Andreasdahlberg/sillycat/hardware/node_unit_exterior/standard_components/aa_battery.SLDPRT

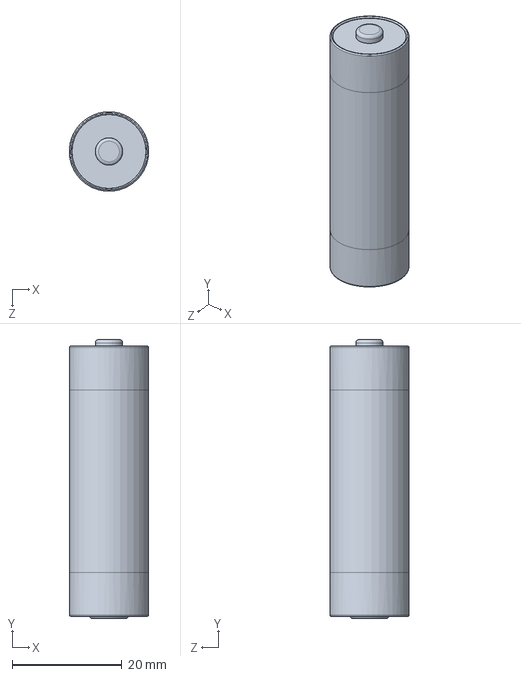
[picture p21: CAD file, 2015-09-07]
hardware/node_unit_exterior/standard_components/aa_battery.SLDPRT
14.5 x 50.9 x 14.5 mm
