Andreasdahlberg/sillycat/hardware/main_unit_exterior/electrical_components/male_header_20.SLDPRT

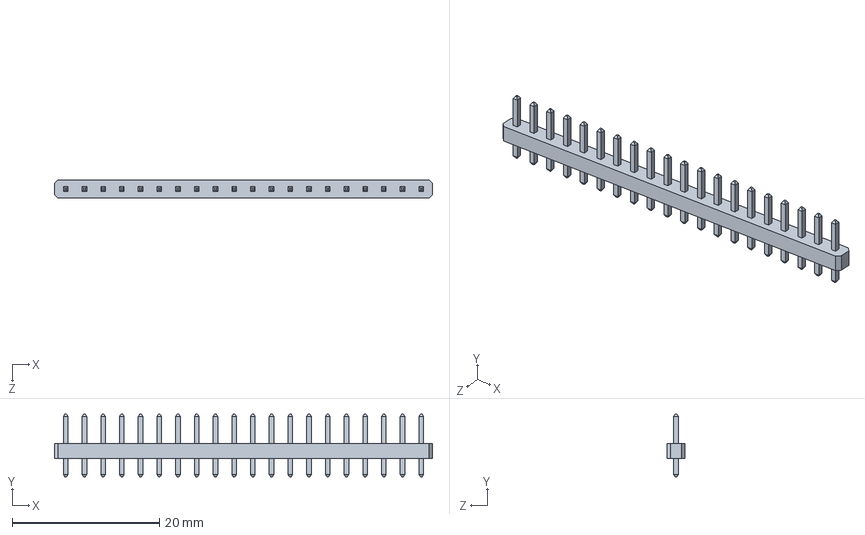
[picture p22: CAD file, 2014-12-17]
hardware/main_unit_exterior/electrical_components/male_header_20.SLDPRT
51.3 x 8.50 x 2.50 mm
