Andreasdahlberg/sillycat/hardware/main_unit_exterior/mechanical_components/front_casing.SLDPRT

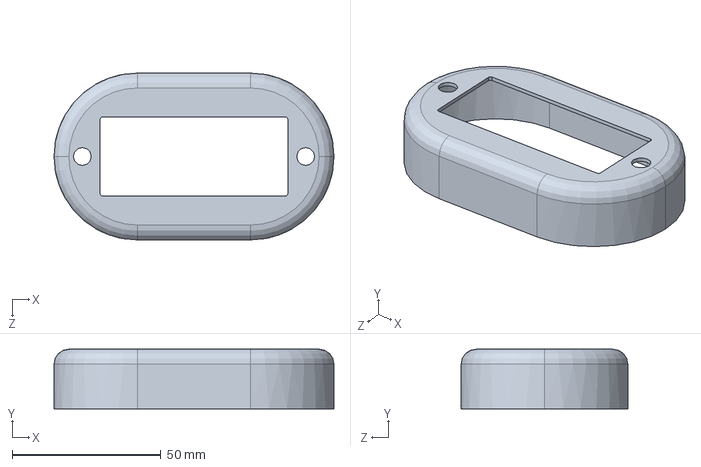
[picture p23: CAD file, 2014-12-17]
hardware/main_unit_exterior/mechanical_components/front_casing.SLDPRT
94.0 x 20.0 x 56.0 mm
