Andreasdahlberg/sillycat/hardware/node_unit_exterior/production_files/casing_end_cover_usb.STL

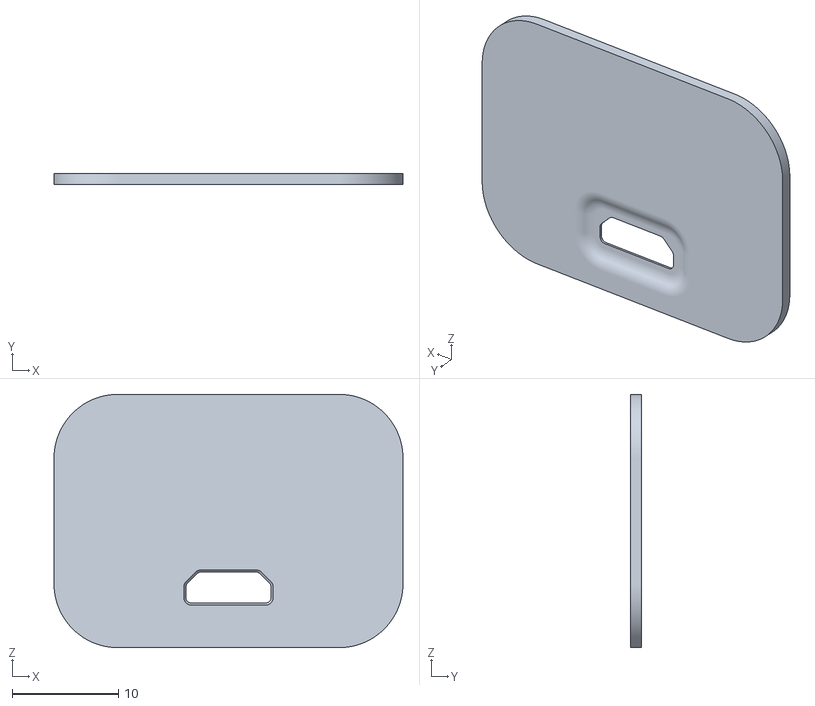
[picture p24: CAD file, 2014-09-30]
hardware/node_unit_exterior/production_files/casing_end_cover_usb.STL
32.8 x 1.00 x 23.8
