Andreasdahlberg/sillycat/hardware/main_unit_exterior/electrical_components/TO-220.SLDPRT

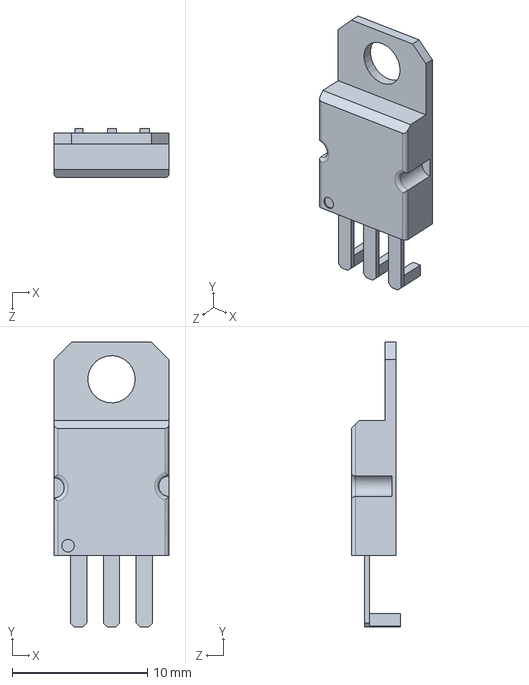
[picture p25: CAD file, 2014-12-17]
hardware/main_unit_exterior/electrical_components/TO-220.SLDPRT
8.50 x 21.1 x 3.66 mm
