Andreasdahlberg/sillycat/hardware/node_unit_exterior/production_files/casing_casing_upper.STL

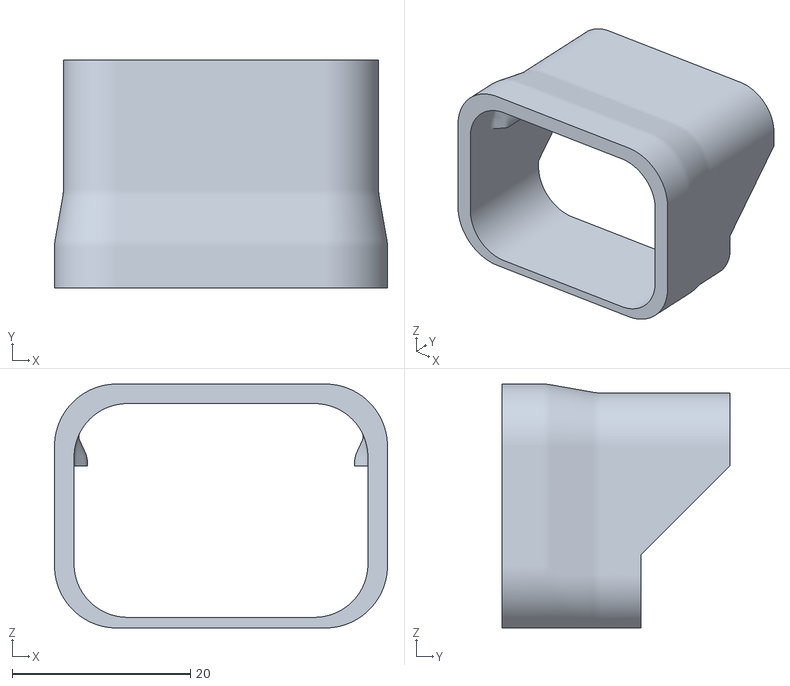
[picture p26: CAD file, 2014-09-30]
hardware/node_unit_exterior/production_files/casing_casing_upper.STL
37.4 x 25.6 x 27.4
