Andreasdahlberg/sillycat/hardware/node_unit_exterior/standard_components/SMA_antenna.SLDPRT

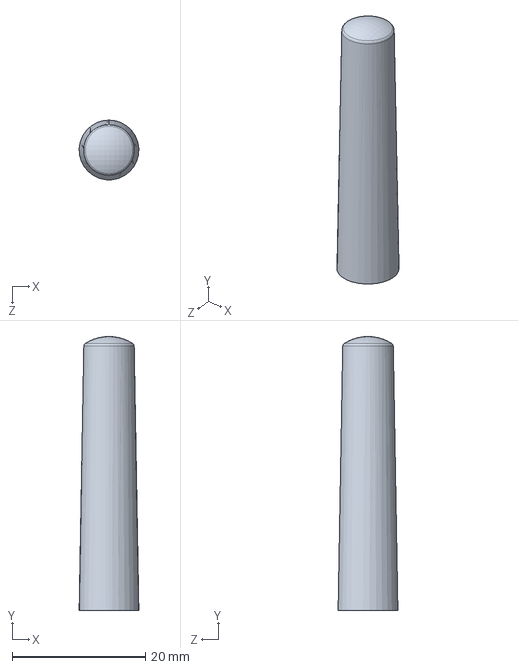
[picture p27: CAD file, 2015-09-06]
hardware/node_unit_exterior/standard_components/SMA_antenna.SLDPRT
8.99 x 41.2 x 9.00 mm
