Andreasdahlberg/sillycat/hardware/main_unit_exterior/electrical_components/NHD_223_OLED_display.SLDPRT

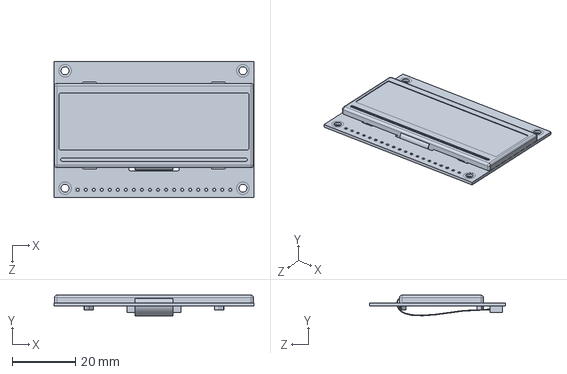
[picture p28: CAD file, 2014-12-17]
hardware/main_unit_exterior/electrical_components/NHD_223_OLED_display.SLDPRT
63.2 x 6.53 x 43.1 mm
