Andreasdahlberg/sillycat/hardware/node_unit_exterior/end_plug_cover.SLDPRT

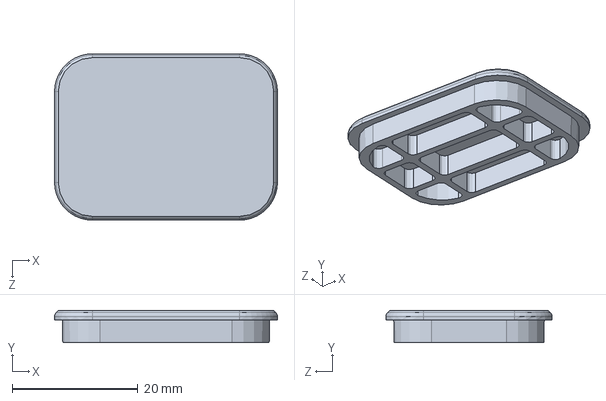
[picture p29: CAD file, 2015-09-07]
hardware/node_unit_exterior/end_plug_cover.SLDPRT
35.4 x 5.10 x 26.4 mm
