Andreasdahlberg/sillycat/hardware/node_unit_exterior/standard_components/DPAK.SLDPRT

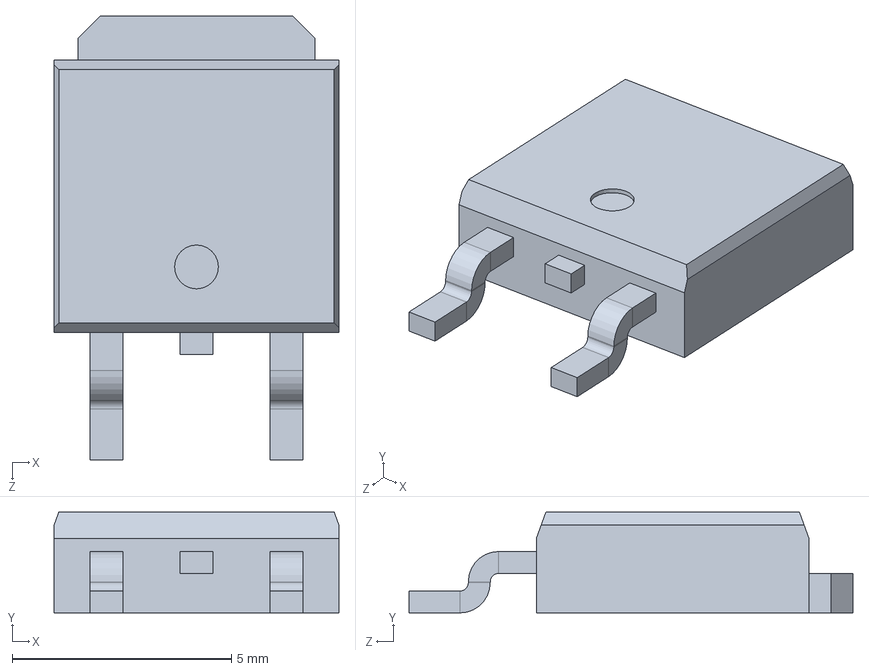
[picture p30: CAD file, 2015-09-06]
hardware/node_unit_exterior/standard_components/DPAK.SLDPRT
6.50 x 2.30 x 10.1 mm
