Andreasdahlberg/sillycat/hardware/node_unit_exterior/end_cover_usb.SLDPRT

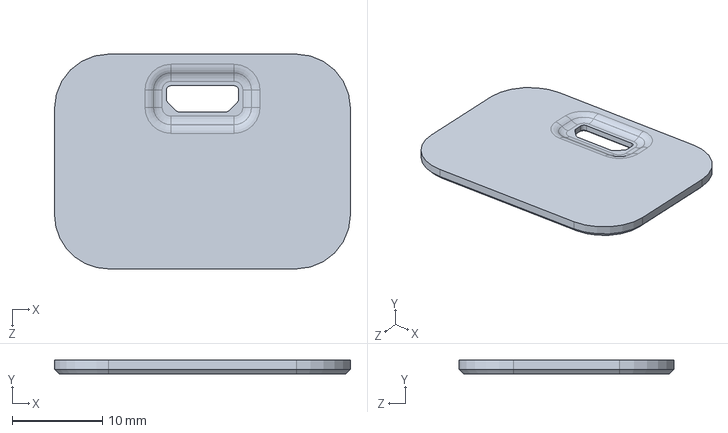
[picture p31: CAD file, 2015-09-07]
hardware/node_unit_exterior/end_cover_usb.SLDPRT
32.8 x 1.50 x 23.8 mm
