Andreasdahlberg/sillycat/hardware/node_unit_exterior/standard_components/nfc_tag.SLDPRT

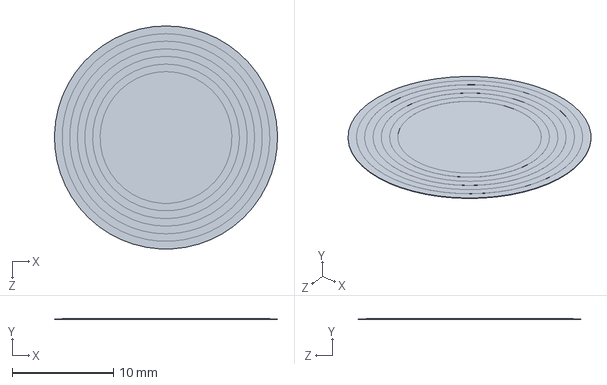
[picture p32: CAD file, 2015-09-05]
hardware/node_unit_exterior/standard_components/nfc_tag.SLDPRT
22.0 x 0.06 x 22.0 mm
