Andreasdahlberg/sillycat/hardware/node_unit_exterior/casing_lower.SLDPRT

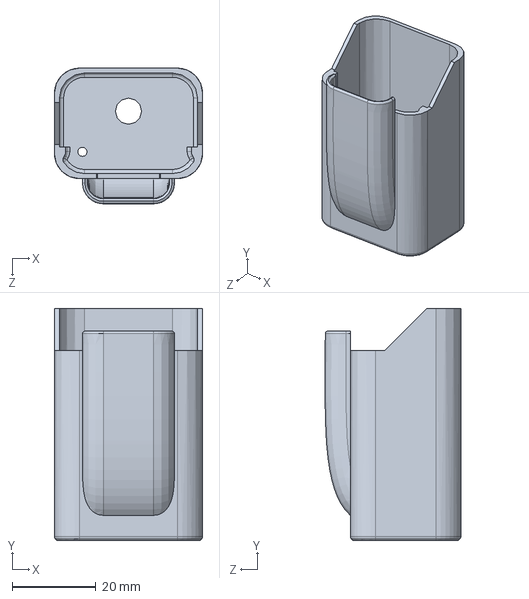
[picture p33: CAD file, 2015-09-05]
hardware/node_unit_exterior/casing_lower.SLDPRT
35.4 x 55.4 x 32.4 mm
