Andreasdahlberg/sillycat/hardware/node_unit_exterior/standard_components/wago_2059_303_casing.SLDPRT

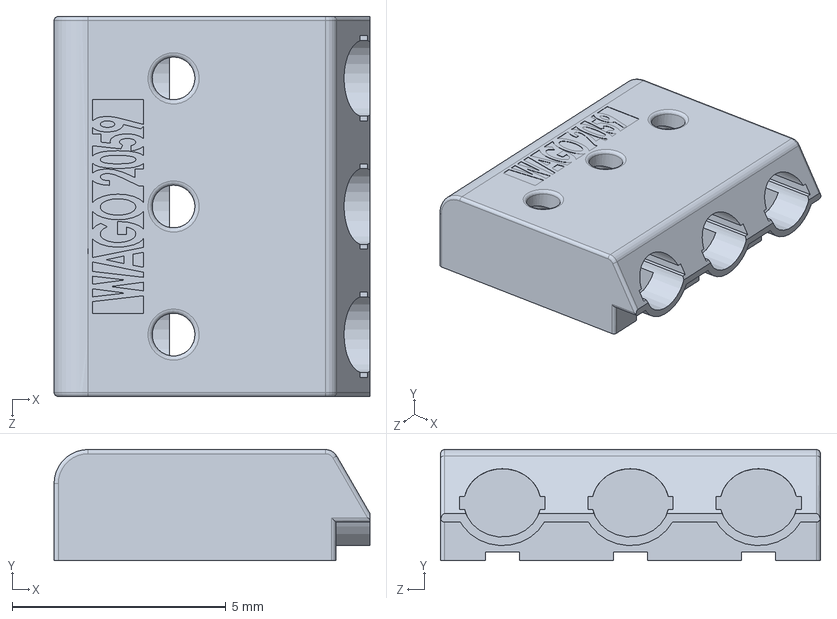
[picture p34: CAD file, 2015-09-05]
hardware/node_unit_exterior/standard_components/wago_2059_303_casing.SLDPRT
7.40 x 2.60 x 8.90 mm
