Andreasdahlberg/sillycat/hardware/node_unit_exterior/casing_upper.SLDPRT

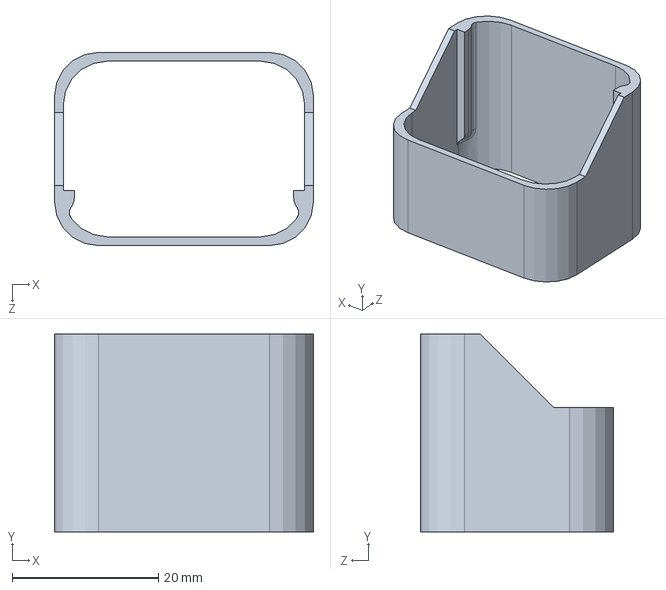
[picture p35: CAD file, 2015-09-05]
hardware/node_unit_exterior/casing_upper.SLDPRT
35.4 x 27.0 x 26.4 mm
