Andreasdahlberg/sillycat/hardware/node_unit_exterior/standard_components/wago_2059_303_pin.SLDPRT

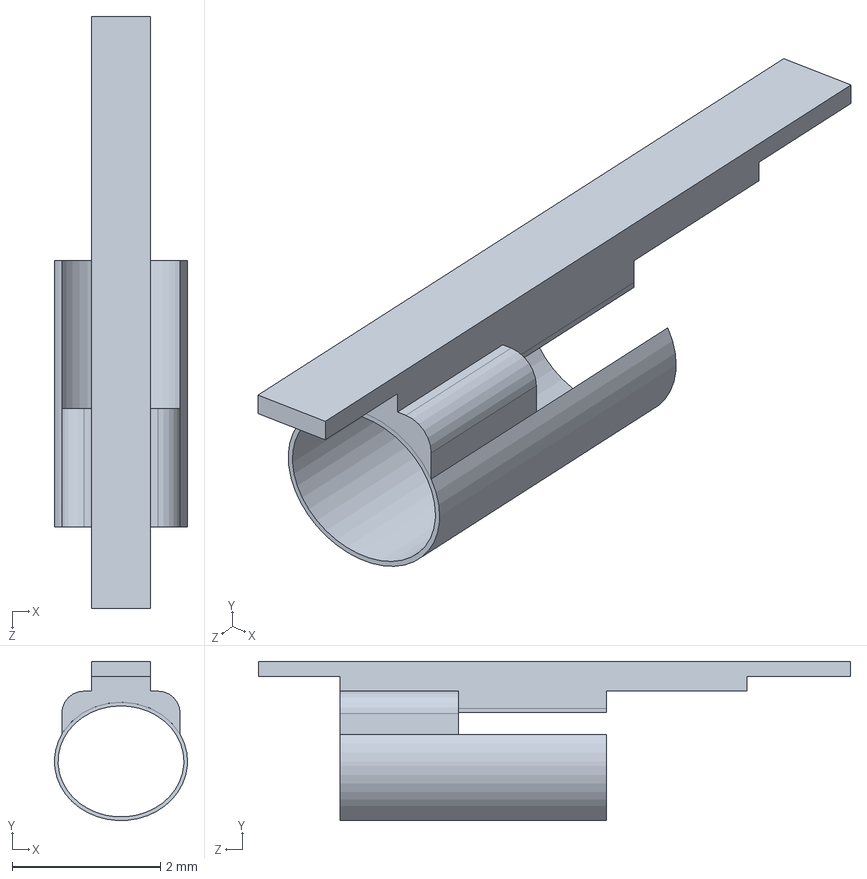
[picture p36: CAD file, 2015-09-05]
hardware/node_unit_exterior/standard_components/wago_2059_303_pin.SLDPRT
1.80 x 2.15 x 8.00 mm
