Andreasdahlberg/sillycat/hardware/node_unit_exterior/dht11_pcb.SLDPRT

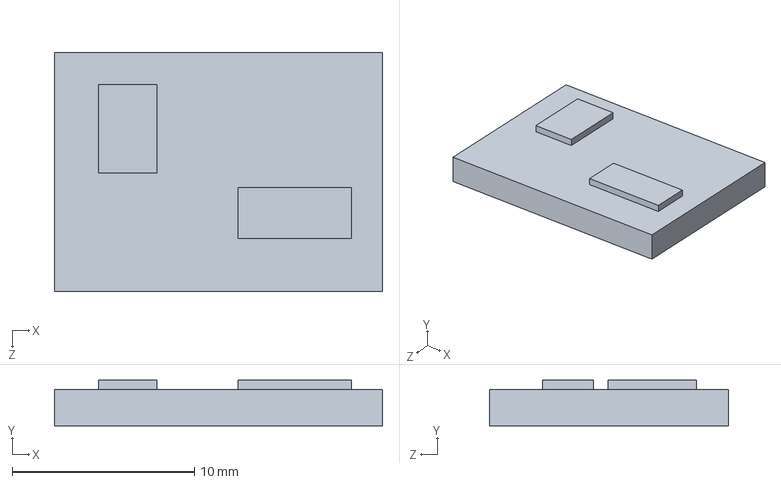
[picture p37: CAD file, 2015-09-05]
hardware/node_unit_exterior/dht11_pcb.SLDPRT
18.0 x 2.50 x 13.1 mm
