Andreasdahlberg/sillycat/hardware/node_unit_exterior/standard_components/micro usb02.SLDPRT

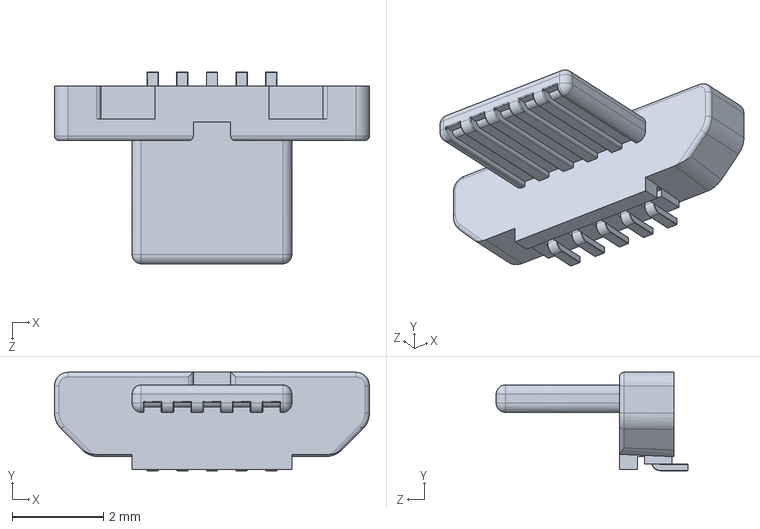
[picture p38: CAD file, 2015-09-05]
hardware/node_unit_exterior/standard_components/micro usb02.SLDPRT
6.90 x 2.16 x 4.20 mm
