Andreasdahlberg/sillycat/hardware/node_unit_exterior/dht11_body.SLDPRT

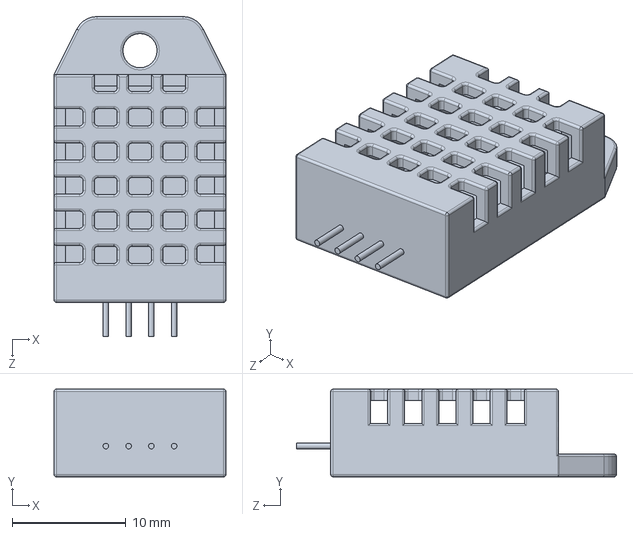
[picture p39: CAD file, 2015-09-05]
hardware/node_unit_exterior/dht11_body.SLDPRT
15.1 x 7.70 x 28.1 mm
