Andreasdahlberg/sillycat/hardware/node_unit_exterior/pcb.SLDPRT

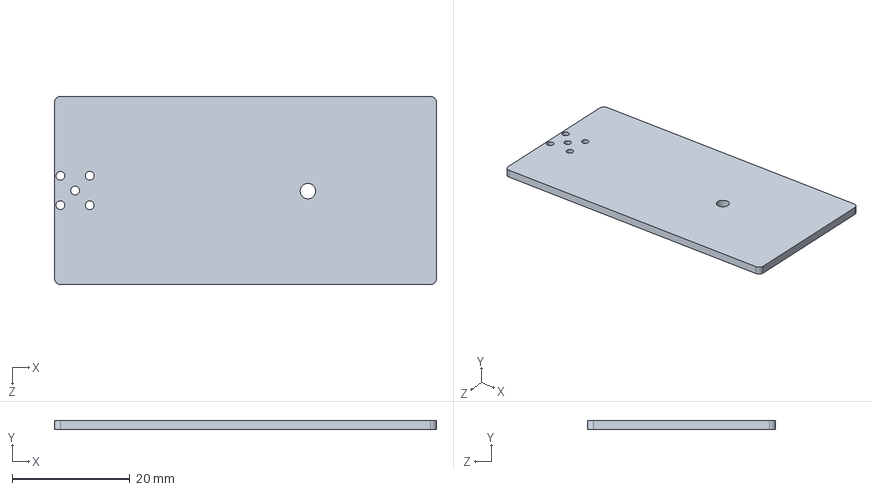
[picture p40: CAD file, 2015-09-05]
hardware/node_unit_exterior/pcb.SLDPRT
65.0 x 1.60 x 32.0 mm
