Andreasdahlberg/sillycat/hardware/node_unit_exterior/standard_components/spring.SLDPRT

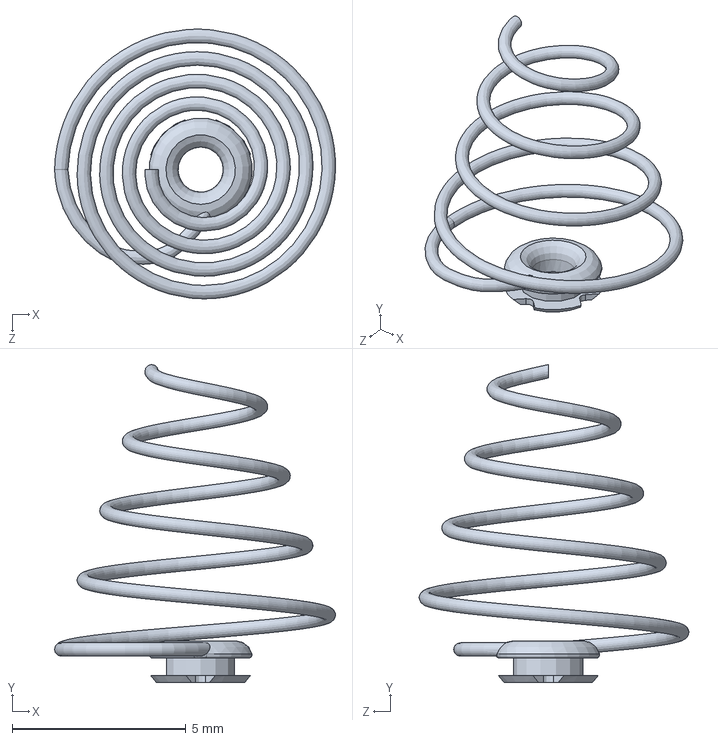
[picture p41: CAD file, 2015-09-05]
hardware/node_unit_exterior/standard_components/spring.SLDPRT
8.08 x 9.14 x 7.76 mm
