Andreasdahlberg/sillycat/hardware/node_unit_exterior/standard_components/end_plug.SLDPRT

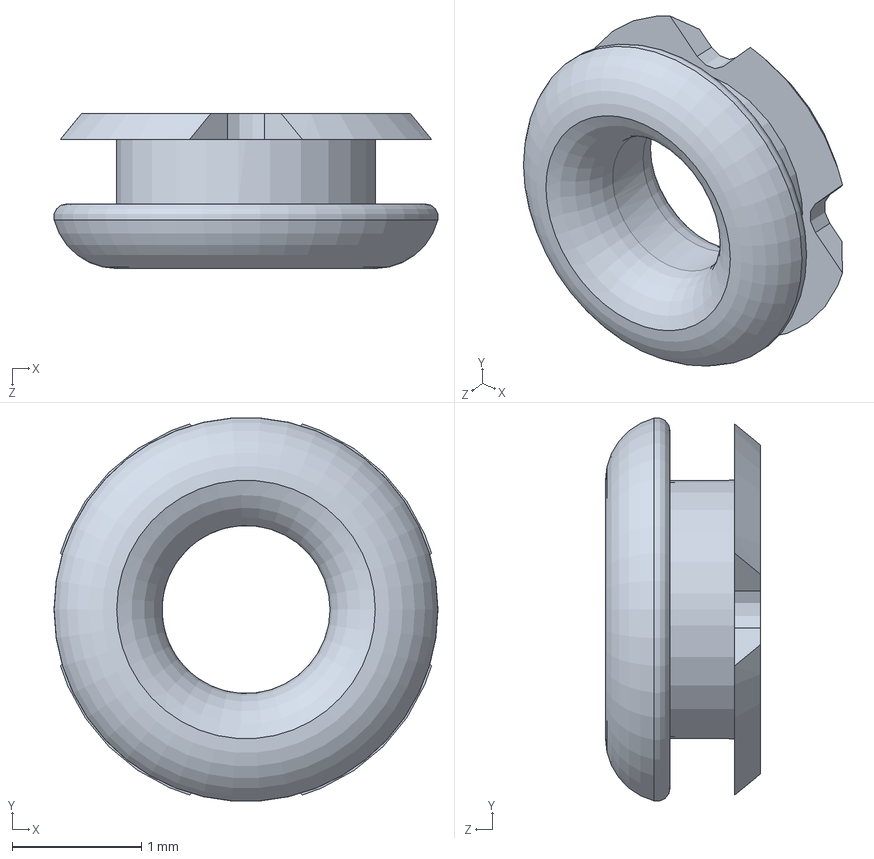
[picture p42: CAD file, 2015-09-05]
hardware/node_unit_exterior/standard_components/end_plug.SLDPRT
2.97 x 2.96 x 1.20 mm
