Andreasdahlberg/sillycat/hardware/node_unit_exterior/rfm69hw.SLDPRT

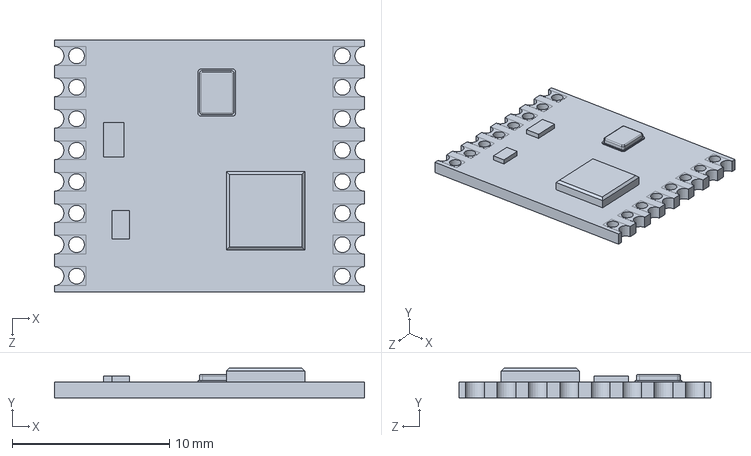
[picture p43: CAD file, 2015-09-05]
hardware/node_unit_exterior/rfm69hw.SLDPRT
19.7 x 1.90 x 16.0 mm
