Andreasdahlberg/sillycat/hardware/node_unit_exterior/standard_components/resistor_1206.SLDPRT

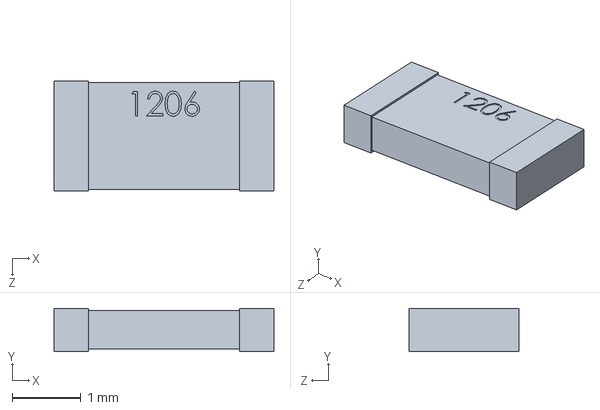
[picture p44: CAD file, 2015-09-05]
hardware/node_unit_exterior/standard_components/resistor_1206.SLDPRT
3.20 x 0.63 x 1.60 mm
