Andreasdahlberg/sillycat/hardware/node_unit_exterior/led_diffuser.SLDPRT

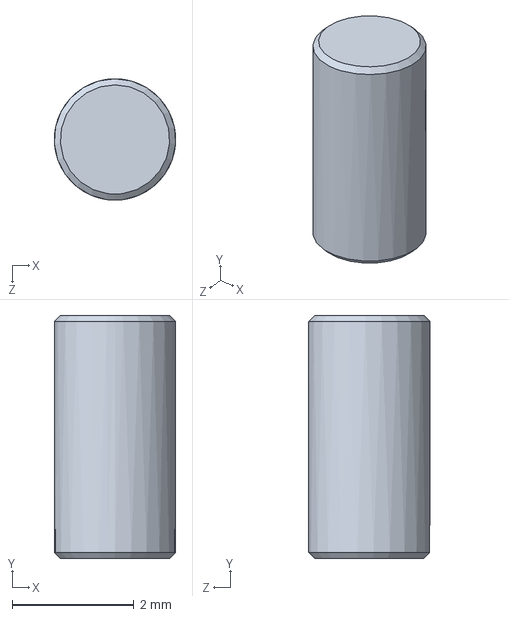
[picture p45: CAD file, 2015-09-05]
hardware/node_unit_exterior/led_diffuser.SLDPRT
2.00 x 4.00 x 2.00 mm
