Andreasdahlberg/sillycat/hardware/node_unit_exterior/standard_components/cap1206.SLDPRT

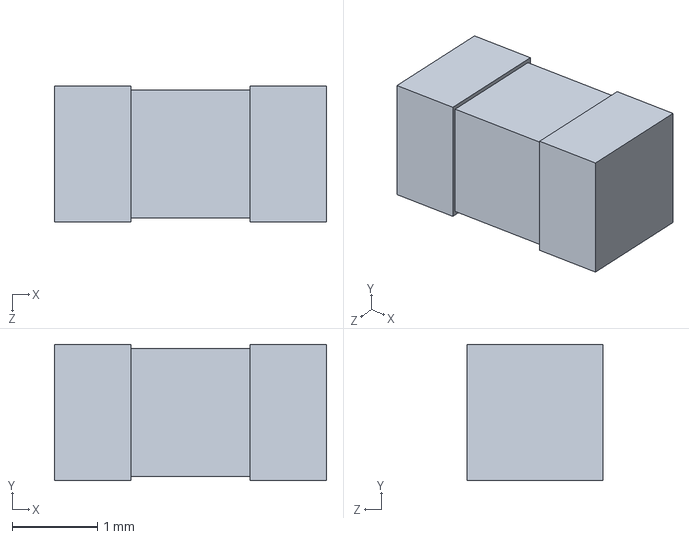
[picture p46: CAD file, 2015-09-05]
hardware/node_unit_exterior/standard_components/cap1206.SLDPRT
3.20 x 1.60 x 1.60 mm
