Andreasdahlberg/sillycat/hardware/node_unit_exterior/standard_components/spring_pin.SLDPRT

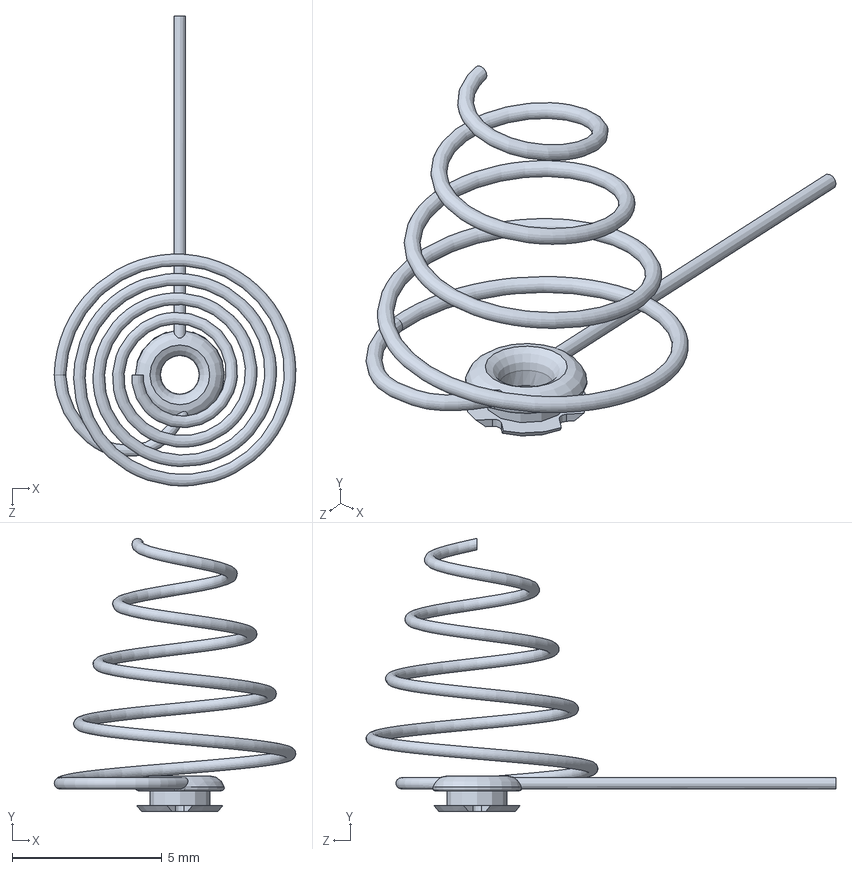
[picture p47: CAD file, 2015-09-05]
hardware/node_unit_exterior/standard_components/spring_pin.SLDPRT
8.08 x 9.14 x 15.7 mm
