Andreasdahlberg/sillycat/hardware/node_unit_exterior/standard_components/TQFP-32.SLDPRT

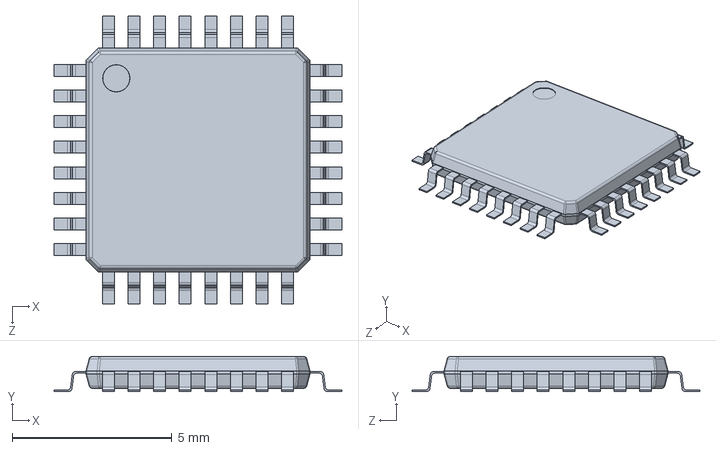
[picture p48: CAD file, 2015-09-05]
hardware/node_unit_exterior/standard_components/TQFP-32.SLDPRT
9.00 x 1.10 x 9.00 mm
