Andreasdahlberg/sillycat/hardware/node_unit_exterior/standard_components/SMA-angled.SLDPRT

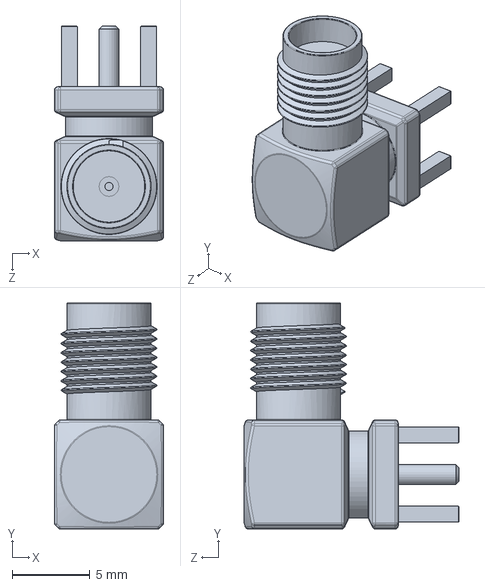
[picture p49: CAD file, 2015-09-05]
hardware/node_unit_exterior/standard_components/SMA-angled.SLDPRT
7.00 x 14.5 x 13.8 mm
