Andreasdahlberg/sillycat/hardware/node_unit_exterior/standard_components/1206_led_blue.SLDPRT

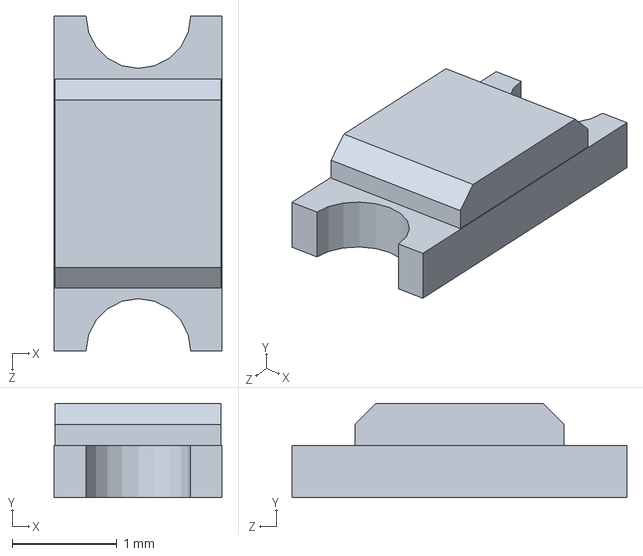
[picture p50: CAD file, 2015-09-05]
hardware/node_unit_exterior/standard_components/1206_led_blue.SLDPRT
1.60 x 0.9 x 3.20 mm
