Andreasdahlberg/sillycat/hardware/node_unit_exterior/standard_components/battery_holder_body.SLDPRT

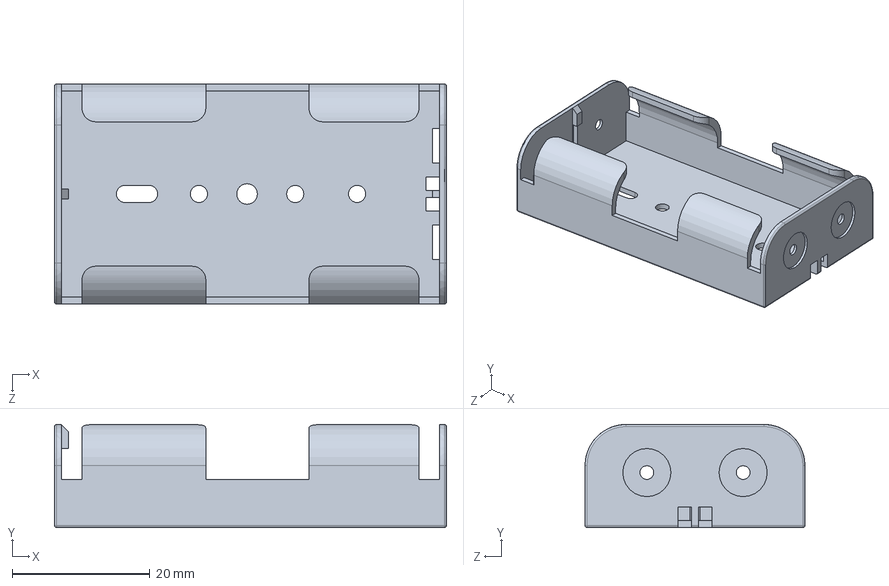
[picture p51: CAD file, 2015-09-05]
hardware/node_unit_exterior/standard_components/battery_holder_body.SLDPRT
57.0 x 15.0 x 32.0 mm
