Andreasdahlberg/sillycat/hardware/node_unit_exterior/standard_components/end_plug_pin.SLDPRT

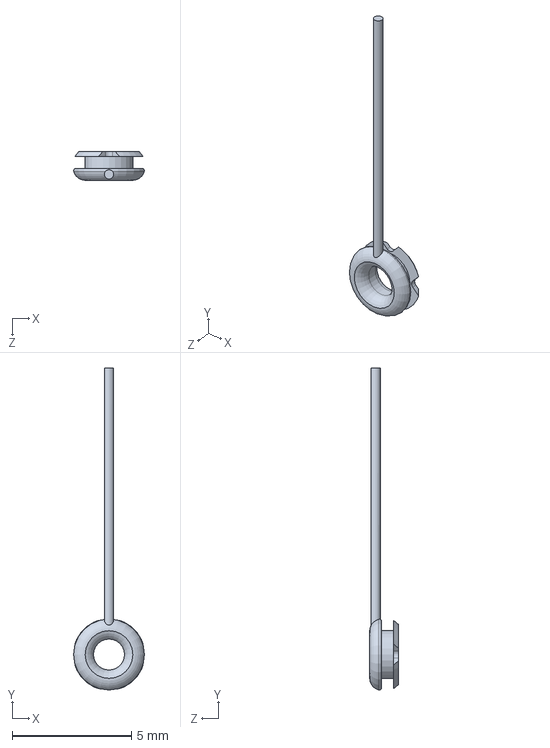
[picture p52: CAD file, 2015-09-05]
hardware/node_unit_exterior/standard_components/end_plug_pin.SLDPRT
2.97 x 13.5 x 1.20 mm
