Andreasdahlberg/sillycat/hardware/node_unit_exterior/standard_components/heatsink_V5618A.SLDPRT

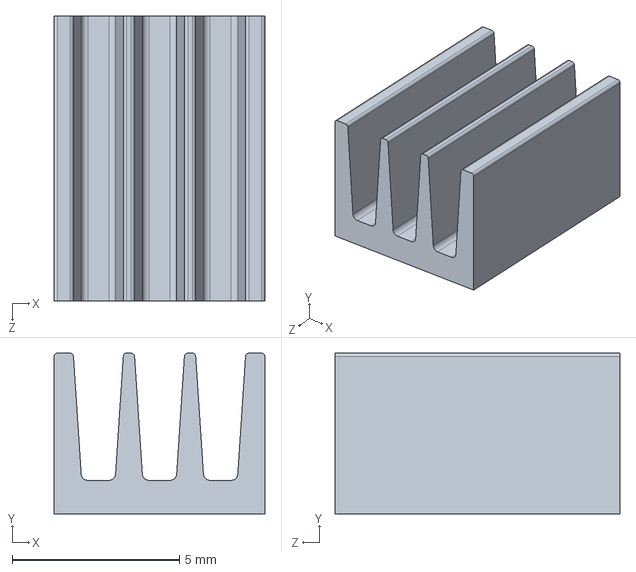
[picture p53: CAD file, 2015-09-05]
hardware/node_unit_exterior/standard_components/heatsink_V5618A.SLDPRT
6.30 x 4.80 x 8.50 mm
