Andreasdahlberg/sillycat/hardware/node_unit_exterior/standard_components/isp_header_6pin.SLDPRT

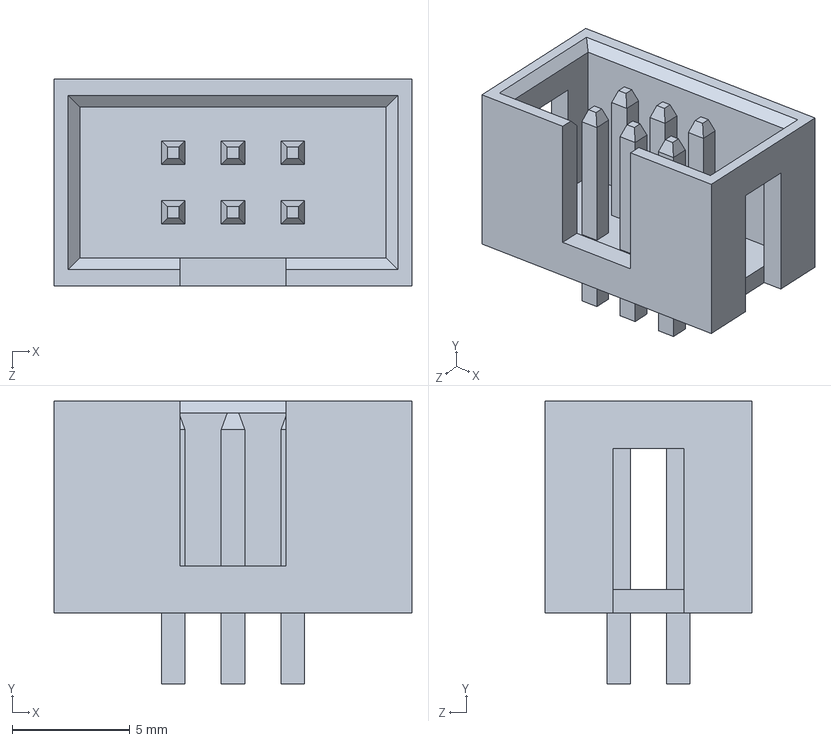
[picture p54: CAD file, 2014-09-03]
hardware/node_unit_exterior/standard_components/isp_header_6pin.SLDPRT
15.2 x 12.0 x 8.80 mm
