Andreasdahlberg/sillycat/hardware/node_unit_exterior/standard_components/USB-Mini-B.SLDPRT

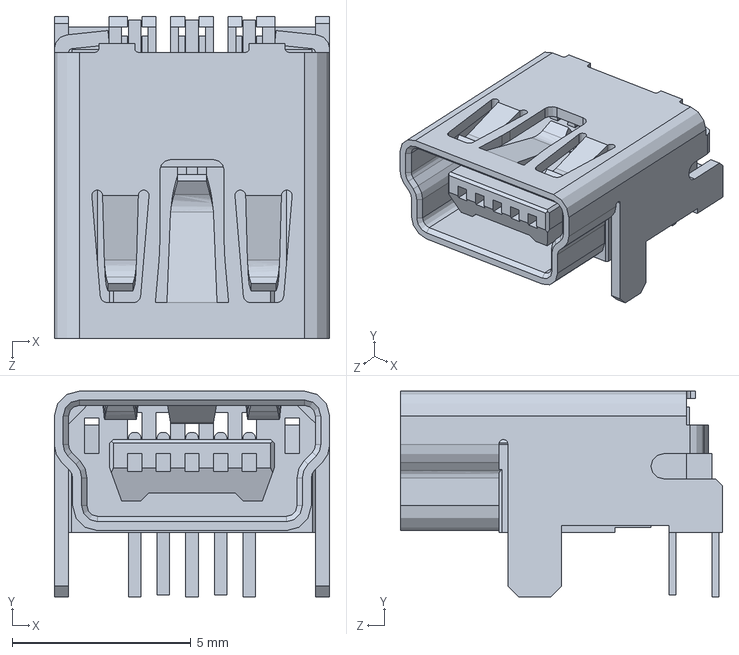
[picture p55: CAD file, 2014-09-03]
hardware/node_unit_exterior/standard_components/USB-Mini-B.SLDPRT
7.70 x 5.75 x 9.00 mm
