Andreasdahlberg/sillycat/firmware/src/main/driver/NTC/driverNTC.c

/**
 * @file   driverNTC.c
 * @Author Andreas Dahlberg (andreas.dahlberg90@gmail.com)
 * @date   2021-04-12 (Last edit)
 * @brief  NTC sensor driver
 *
 * Driver for NTC sensors.
 */

/*
This file is part of SillyCat firmware.

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
You should have received a copy of the GNU General Public License
along with SillyCat firmware.  If not, see <http://www.gnu.org/licenses/>.
*/

//////////////////////////////////////////////////////////////////////////
//INCLUDES
//////////////////////////////////////////////////////////////////////////

//NOTE: Include before all other headers
#include "common.h"

#include <avr/pgmspace.h>
#include "ADC.h"
#include "Sensor.h"
#include "Timer.h"
#include "Filter.h"
#include "libDebug.h"
#include "driverNTC.h"

//////////////////////////////////////////////////////////////////////////
//DEFINES
//////////////////////////////////////////////////////////////////////////

#define SAMPLE_PERIOD_MS 100
#define LUT_SIZE 819

//////////////////////////////////////////////////////////////////////////
//TYPE DEFINITIONS
//////////////////////////////////////////////////////////////////////////

enum lookup_table_type {GENERIC, MF52};

struct ntc_sensor_t
{
    struct sensor_t base;
    struct
    {
        struct adc_channel_t channel;
        uint8_t index;
    } adc;
    struct filter_t filter;
    uint32_t timer;
    enum lookup_table_type lut_type;
};

struct lookup_table_t
{
    uint16_t offset;
    uint16_t temperatures[LUT_SIZE];
};

//////////////////////////////////////////////////////////////////////////
//LOCAL FUNCTION PROTOTYPES
//////////////////////////////////////////////////////////////////////////

static void Update(struct sensor_t *super_p);
static bool GetTemperature(struct ntc_sensor_t *self_p, int16_t *temperature_p);
static bool ADCValueToTemperature(uint16_t adc_value, int16_t *temperature_p, size_t lut_index);
static bool IsValid(uint16_t adc_value, size_t lut_index);
static int16_t FilterTemperature(struct ntc_sensor_t *self_p, int16_t temperature);

//////////////////////////////////////////////////////////////////////////
//VARIABLES
//////////////////////////////////////////////////////////////////////////

static const struct lookup_table_t ntc_lut[2] PROGMEM =
{
    {
        .offset = 120,
        .temperatures = {
            -201, -199, -197, -195, -194, -192, -190, -188, -187, -185, -183, -181, -180, -178,
                -176, -175, -173, -172, -170, -168, -167, -165, -163, -162, -160, -159, -157, -156,
                -154, -152, -151, -149, -148, -146, -145, -143, -142, -140, -139, -137, -136, -134,
                -133, -131, -130, -129, -127, -126, -124, -123, -121, -120, -119, -117, -116, -114,
                -113, -112, -110, -109, -107, -106, -105, -103, -102, -101, -99, -98, -97, -95, -94,
                -93, -91, -90, -89, -87, -86, -85, -83, -82, -81, -79, -78, -77, -76, -74, -73, -72,
                -71, -69, -68, -67, -66, -64, -63, -62, -61, -59, -58, -57, -56, -54, -53, -52, -51,
                -50, -48, -47, -46, -45, -43, -42, -41, -40, -39, -38, -36, -35, -34, -33, -32, -30,
                -29, -28, -27, -26, -25, -23, -22, -21, -20, -19, -18, -17, -15, -14, -13, -12, -11,
                -10, -9, -7, -6, -5, -4, -3, -2, -1, 0, 2, 3, 4, 5, 6, 7, 8, 9, 10, 11, 13, 14, 15, 16,
                17, 18, 19, 20, 21, 22, 23, 25, 26, 27, 28, 29, 30, 31, 32, 33, 34, 35, 36, 37, 39, 40,
                41, 42, 43, 44, 45, 46, 47, 48, 49, 50, 51, 52, 53, 54, 55, 56, 57, 59, 60, 61, 62, 63,
                64, 65, 66, 67, 68, 69, 70, 71, 72, 73, 74, 75, 76, 77, 78, 79, 80, 81, 82, 83, 84, 85,
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
            .Update = Update
        },
        .adc = {
            .index = 0x06
        },
        .lut_type = GENERIC
    },
    {
        .base =
        {
            .Update = Update
        },
        .adc = {
            .index = 0x07
        },
        .lut_type = MF52
    }
};

//////////////////////////////////////////////////////////////////////////
//FUNCTIONS
//////////////////////////////////////////////////////////////////////////

void driverNTC_Init(void)
{
    for (size_t i = 0; i < ElementsIn(ntc_sensors); ++i)
    {
        ADC_InitChannel(&ntc_sensors[i].adc.channel, ntc_sensors[i].adc.index);
    }

    INFO("NTC sensors initialized");
}

struct sensor_t *driverNTC_GetSensor(size_t id)
{
    sc_assert(id < ElementsIn(ntc_sensors));

    return (struct sensor_t *)&ntc_sensors[id];
}

//////////////////////////////////////////////////////////////////////////
//LOCAL FUNCTIONS
//////////////////////////////////////////////////////////////////////////

static void Update(struct sensor_t *super_p)
{
    struct ntc_sensor_t *self_p = (struct ntc_sensor_t *)super_p;

    if (Timer_TimeDifference(self_p->timer) > SAMPLE_PERIOD_MS)
    {
        int16_t temperature;

        if (GetTemperature(self_p, &temperature))
        {
            self_p->base.value = FilterTemperature(self_p, temperature);
            self_p->base.valid = true;
        }
        else
        {
            self_p->base.valid = false;
        }

        self_p->timer = Timer_GetMilliseconds();
    }
}

static bool GetTemperature(struct ntc_sensor_t *self_p, int16_t *temperature_p)
{
    uint16_t adc_value;

    ADC_Convert(&self_p->adc.channel, &adc_value, 1);
    return ADCValueToTemperature(adc_value, temperature_p, self_p->lut_type);
}

static bool ADCValueToTemperature(uint16_t adc_value, int16_t *temperature_p, size_t lut_index)
{
    if (IsValid(adc_value, lut_index))
    {
        const uint16_t offset = pgm_read_word(&ntc_lut[lut_index].offset);

        *temperature_p = pgm_read_word(&ntc_lut[lut_index].temperatures[adc_value - offset]);
        return true;
    }
    else
    {
        return false;
    }
}

static bool IsValid(uint16_t adc_value, size_t lut_index)
{
    const uint16_t offset = pgm_read_word(&ntc_lut[lut_index].offset);

    return (adc_value >= offset) &&
           (adc_value - offset < ElementsIn(ntc_lut[lut_index].temperatures));
}

static int16_t FilterTemperature(struct ntc_sensor_t *self_p, int16_t temperature)
{
    if (Filter_IsInitialized(&self_p->filter))
    {
        Filter_Process(&self_p->filter, temperature);
    }
    else
    {
        Filter_Init(&self_p->filter, temperature, FILTER_ALPHA(0.1));
    }

    return Filter_Output(&self_p->filter);
}
