Andreasdahlberg/sillycat/firmware/src/node/Sensor.c

/**
 * @file   Sensor.c
 * @Author Andreas Dahlberg (andreas.dahlberg90@gmail.com)
 * @date   2020-03-10 (Last edit)
 * @brief  Implementation of Sensor module
 *
 * Detailed description of file.
 */

/*
This file is part of SillyCat firmware.

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
You should have received a copy of the GNU General Public License
along with SillyCat firmware.  If not, see <http://www.gnu.org/licenses/>.
*/

//////////////////////////////////////////////////////////////////////////
//INCLUDES
//////////////////////////////////////////////////////////////////////////

#include "common.h"
#include "libDebug.h"
#include "driverDHT22.h"
#include "Sensor.h"
#include "RTC.h"
#include "FIFO.h"
#include "ErrorHandler.h"

//////////////////////////////////////////////////////////////////////////
//DEFINES
//////////////////////////////////////////////////////////////////////////

#define READING_BUFFER_SIZE 4

//////////////////////////////////////////////////////////////////////////
//TYPE DEFINITIONS
//////////////////////////////////////////////////////////////////////////

//////////////////////////////////////////////////////////////////////////
//VARIABLES
//////////////////////////////////////////////////////////////////////////

static sensor_data_type reading_buffer[READING_BUFFER_SIZE];
static struct fifo_t reading_fifo;

//////////////////////////////////////////////////////////////////////////
//LOCAL FUNCTION PROTOTYPES
//////////////////////////////////////////////////////////////////////////

//////////////////////////////////////////////////////////////////////////
//FUNCTIONS
//////////////////////////////////////////////////////////////////////////

///
/// @brief Init the sensor module.
///
/// @param  None
/// @return None
///
void Sensor_Init(void)
{
    reading_fifo = FIFO_New(reading_buffer);

    INFO("Init done");
}

///
/// @brief Update the internal state of the sensor module.
///
/// @param  None
/// @return None
///
void Sensor_Update(void)
{
    if (driverDHT22_IsMeasurmentValid())
    {
        sensor_data_type reading;
        reading.temperature = driverDHT22_GetTemperature();
        reading.humidity = driverDHT22_GetHumidity();
        driverDHT22_ClearValidFlag();
        if (!RTC_GetCurrentTime(&reading.timestamp))
        {
            // Log error and continue, an invalid timestamp is not critical.
            ErrorHandler_LogError(RTC_FAIL, 0);

            ERROR("Failed to get timestamp.");
        }

        // Discard the oldest reading if the buffer is full.
        if (FIFO_IsFull(&reading_fifo))
        {
            sensor_data_type dummy_reading;
            FIFO_Pop(&reading_fifo, &dummy_reading);

            WARNING("FIFO is full, discarding oldest entry.");
        }
        FIFO_Push(&reading_fifo, &reading);

        event_t event;
        event = Event_New(EVENT_RHT_AVAILABLE);
        Event_Trigger(&event);

        INFO("RHT: %i:%i", reading.humidity, reading.temperature);
    }
    return;
}

///
/// @brief Get a sensor reading from the reading FIFO.
///
/// @param  *reading Pointer to struct where the reading will be stored.
/// @return bool True if a reading is available.
///
bool Sensor_GetReading(sensor_data_type *reading)
{
    sc_assert(reading != NULL);

    return FIFO_Pop(&reading_fifo, reading);
}

///
/// @brief Handle wake up events.
///
/// @param  *event Pointer to triggered event.
/// @return None
///
void Sensor_WakeUp(const event_t *event __attribute__ ((unused)))
{
    sc_assert(event != NULL);

    driverDHT22_StartMeasurement();
    return;
}

///
/// @brief Handle sleep events.
///
/// @param  *event Pointer to triggered event.
/// @return None
///
void Sensor_Sleep(const event_t *event __attribute__ ((unused)))
{
    sc_assert(event != NULL);

    while (!driverDHT22_IsIdle())
    {
        driverDHT22_Update();
    }
}

//////////////////////////////////////////////////////////////////////////
//LOCAL FUNCTIONS
//////////////////////////////////////////////////////////////////////////
