Andreasdahlberg/sillycat/firmware/src/node/Power.c

/**
 * @file   Power.c
 * @Author Andreas Dahlberg (andreas.dahlberg90@gmail.com)
 * @date   2019-04-30 (Last edit)
 * @brief  Implementation of the power management module.
 */

/*
This file is part of SillyCat firmware.

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
You should have received a copy of the GNU General Public License
along with SillyCat firmware.  If not, see <http://www.gnu.org/licenses/>.
*/

//////////////////////////////////////////////////////////////////////////
//INCLUDES
//////////////////////////////////////////////////////////////////////////

#include "common.h"
#include "libDebug.h"
#include "libPower.h"
#include "driverCharger.h"
#include "Power.h"
#include "Event.h"
#include "Battery.h"

//////////////////////////////////////////////////////////////////////////
//DEFINES
//////////////////////////////////////////////////////////////////////////

//////////////////////////////////////////////////////////////////////////
//TYPE DEFINITIONS
//////////////////////////////////////////////////////////////////////////

typedef enum
{
    POWER_INIT = 0,
    POWER_NORMAL,
    POWER_LOW,
    POWER_CRITICAL,
    POWER_CHARGING,
    POWER_CONNECTED
} power_state_type;

//////////////////////////////////////////////////////////////////////////
//VARIABLES
//////////////////////////////////////////////////////////////////////////

static power_state_type battery_state;

//////////////////////////////////////////////////////////////////////////
//LOCAL FUNCTION PROTOTYPES
//////////////////////////////////////////////////////////////////////////

static void BatteryMonitoringSM(void);

//////////////////////////////////////////////////////////////////////////
//FUNCTIONS
//////////////////////////////////////////////////////////////////////////

void Power_Init(void)
{
    battery_state = POWER_NORMAL;

    return;
}

void Power_Update(void)
{
    BatteryMonitoringSM();
    return;
}

void Power_WakeUp(const event_t *event_p __attribute__ ((unused)))
{
    sc_assert(event_p != NULL);

    DEBUG("Battery voltage: %u\r\n", driverCharger_GetBatteryVoltage());
    DEBUG("Charger connected: %u\r\n", (uint8_t)driverCharger_IsConnected());
    DEBUG("Charging: %u\r\n", (uint8_t)driverCharger_IsCharging());
    return;
}
//////////////////////////////////////////////////////////////////////////
//LOCAL FUNCTIONS
//////////////////////////////////////////////////////////////////////////

static void BatteryMonitoringSM(void)
{
    switch (battery_state)
    {
        case POWER_NORMAL:
            if (driverCharger_IsCharging() == true)
            {
                INFO("Charging started");
                event_t event = Event_New(EVENT_BATTERY_CHARGING_STARTED);
                Event_Trigger(&event);
                battery_state = POWER_CHARGING;
            }
            else if (driverCharger_GetBatteryVoltage() < BATTERY_LOW_VOLTAGE_MV)
            {
                INFO("Low battery voltage[%u mV]", driverCharger_GetBatteryVoltage());
                event_t event = Event_New(EVENT_BATTERY_LOW);
                Event_Trigger(&event);
                battery_state = POWER_LOW;
            }
            break;

        case POWER_LOW:
            if (driverCharger_IsCharging() == true)
            {
                INFO("Charging started");
                event_t event = Event_New(EVENT_BATTERY_CHARGING_STARTED);
                Event_Trigger(&event);
                battery_state = POWER_CHARGING;
            }
            else if (driverCharger_GetBatteryVoltage() < BATTERY_CRITICAL_VOLTAGE_MV)
            {
                WARNING("Critical battery voltage");
                event_t event = Event_New(EVENT_BATTERY_CRITICAL);
                Event_Trigger(&event);
                battery_state = POWER_CRITICAL;
            }
            break;

        case POWER_CRITICAL:
            if (driverCharger_IsCharging() == true)
            {
                INFO("Charging started");
                event_t event = Event_New(EVENT_BATTERY_CHARGING_STARTED);
                Event_Trigger(&event);
                battery_state = POWER_CHARGING;
            }
            break;

        case POWER_CHARGING:
            if (driverCharger_IsCharging() == false)
            {
                INFO("Charging stopped");
                event_t event = Event_New(EVENT_BATTERY_CHARGING_STOPPED);
                Event_Trigger(&event);
                battery_state = POWER_CONNECTED;
            }
            break;

        case POWER_CONNECTED:
            if (driverCharger_IsCharging() == true)
            {
                INFO("Charging started");
                event_t event = Event_New(EVENT_BATTERY_CHARGING_STARTED);
                Event_Trigger(&event);
                battery_state = POWER_CHARGING;
            }

            if (driverCharger_IsConnected() == false)
            {
                INFO("Charger disconnected");
                event_t event = Event_New(EVENT_BATTERY_CHARGER_DISCONNECTED);
                Event_Trigger(&event);
                battery_state = POWER_NORMAL;
            }
            break;

        default:
            sc_assert_fail();
    }

    return;
}

//////////////////////////////////////////////////////////////////////////
//LOCAL FUNCTIONS
//////////////////////////////////////////////////////////////////////////
