Andreasdahlberg/sillycat/firmware/src/node/MCP79510Registers.h

/**
 * @file   MCP79510Registers.h
 * @Author Andreas Dahlberg (andreas.dahlberg90@gmail.com)
 * @date   2016-05-07 (Last edit)
 * @brief  Registers and bit defines for MCP79510.
 *
 * Detailed description of file.
 */

/*
This file is part of SillyCat firmware.

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
You should have received a copy of the GNU General Public License
along with SillyCat firmware.  If not, see <http://www.gnu.org/licenses/>.
*/

#ifndef MCP79510REGISTERS_H_
#define MCP79510REGISTERS_H_

//////////////////////////////////////////////////////////////////////////
//DEFINES
//////////////////////////////////////////////////////////////////////////

//Instructions
#define INST_EEREAD  0x03    //Read data from EE memory array beginning at selected address
#define INST_EEWRITE 0x02    //Write data to EE memory array beginning at selected address
#define INST_EEWRDI  0x04    //Reset the write enable latch (disable write operations)
#define INST_EEWREN  0x06    //Set the write enable latch (enable write operations)
#define INST_SRREAD  0x05    //Read STATUS register
#define INST_SRWRITE 0x01    //Write STATUS register
#define INST_READ    0x13    //Read RTCC/SRAM array beginning at selected address
#define INST_WRITE   0x12    //Write RTCC/SRAM data to memory array beginning at selected address
#define INST_UNLOCK  0x14    //Unlock ID Locations
#define INST_IDWRITE 0x32    //Write to the ID Locations
#define INST_IDREAD  0x33    //Read the ID Locations
#define INST_CLRRAM  0x54    //Clear RAM Location to ‘0’

//Time and configuration(TC) registers
#define REG_TC_SEC_CENT     0x00    //Hundredths of seconds
#define REG_TC_SEC          0x01    //Seconds
#define REG_TC_MIN          0x02    //Minutes
#define REG_TC_HOUR         0x03    //Hours
#define REG_TC_DAY          0x04    //Day
#define REG_TC_DATE         0x05    //Date
#define REG_TC_MONTH        0x06    //Month
#define REG_TC_YEAR         0x07    //Year
#define REG_TC_CONTROL      0x08    //Control register
#define REG_TC_CALIBRATION  0x09    //Calibration

//Alarm 0 Registers
#define REG_ALARM0_SEC      0x0C
#define REG_ALARM0_MIN      0x0D
#define REG_ALARM0_HOUR     0x0E
#define REG_ALARM0_DAY      0x0F
#define REG_ALARM0_DATE     0x10
#define REG_ALARM0_MONTH    0x11

//Alarm 1 Registers
#define REG_ALARM1_SEC_CENT 0x12
#define REG_ALARM1_SEC      0x13
#define REG_ALARM1_MIN      0x14
#define REG_ALARM1_HOUR     0x15
#define REG_ALARM1_DAY      0x16
#define REG_ALARM1_DATE     0x17

//Power-Down Time-Stamp Registers
#define REG_PD_MIN      0x18
#define REG_PD_HOUR     0x19
#define REG_PD_DATE     0x1A
#define REG_PD_MONTH    0x1B

//Power-Up Time-Stamp Registers
#define REG_PU_MIN      0x1C
#define REG_PU_HOUR     0x1D
#define REG_PU_DATE     0x1E
#define REG_PU_MONTH    0x1F

#define SRAM_ADDRESS 0x20

#define REG_TC_SEC_OSC_BIT 0x07

#define REG_TC_HOUR_MODE_BIT 0x06

#define REG_TC_MONTH_LP_BIT 0x05

#define REG_TC_DAY_OSCON_BIT    0x05
#define REG_TC_DAY_VBAT_BIT     0x04
#define REG_TC_DAY_VBATEN_BIT   0x03

#define REG_TC_CONTROL_EXTOSC_BIT   0x03
#define REG_TC_CONTROL_ALM0_BIT     0x04
#define REG_TC_CONTROL_ALM1_BIT     0x05
#define REG_TC_CONTROL_SQWE_BIT     0x06
#define REG_TC_CONTROL_OUT_BIT      0x07

#define REG_ALARM_DAY_ALM0IF_BIT    0x03
#define REG_ALARM_DAY_ALM0C0_BIT    0x04
#define REG_ALARM_DAY_ALM0C1_BIT    0x05
#define REG_ALARM_DAY_ALM0C2_BIT    0x06

#endif /* MCP79510REGISTERS_H_ */
