Andreasdahlberg/sillycat/software/DisplayView.py

#!/usr/bin/env python3
# -*- coding: utf-8 -*
#
# This file is part of SillyCat Development Tools.
#
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
import os
import time
import math
import struct

from PyQt5 import QtGui, QtCore, QtWidgets

__author__ = 'andreas.dahlberg90@gmail.com (Andreas Dahlberg)'
__version__ = '0.1.0'

VRAM_PAGES = 4
VRAM_COLUMNS = 128
VRAM_SIZE = (VRAM_PAGES * VRAM_COLUMNS)


def create_bitmap_image(rows, w):
    mult4 = lambda n: int(math.ceil(n / 4)) * 4
    mult8 = lambda n: int(math.ceil(n / 8)) * 8
    lh = lambda n: struct.pack("<h", n)
    li = lambda n: struct.pack("<i", n)

    h, wB = len(rows), int(mult8(w) / 8)
    s, pad = li(mult4(wB) * h + 0x20), [0] * (mult4(wB) - wB)
    s = li(mult4(w) * h + 0x20)
    return (b"BM" + s + b"\x00\x00\x00\x00\x20\x00\x00\x00\x0C\x00\x00\x00" +
            lh(w) + lh(h) + b"\x01\x00\x01\x00\xff\xff\xff\x00\x00\x00" +
            b"".join([bytes(row + pad) for row in reversed(rows)]))


class DisplayPixmap(QtWidgets.QLabel):

    def __init__(self):
        super(DisplayPixmap, self).__init__()


class DisplayView(QtWidgets.QLabel):
    new_pixel = QtCore.pyqtSignal(QtCore.QPoint)

    def __init__(self, path):
        super(DisplayView, self).__init__()
        self._pixmap = QtGui.QPixmap()
        self.setPixmap(self._pixmap)

        self.setMouseTracking(True)

        self.pos_x = 0
        self.pos_y = 0

        self.path = path

    def mouseMoveEvent(self, event):
        mouse_position = event.pos()

        x_pos = math.floor(mouse_position.x() / 3)
        if x_pos > 127:
            x_pos = 127

        y_pos = math.floor(mouse_position.y() / 3)
        if y_pos > 30:
            y_pos = 30

        scaled_point = QtCore.QPoint(x_pos, y_pos)
        self.new_pixel.emit(scaled_point)

    def set_pixel(self, x, y):
        self.pos_x = x
        self.pos_y = y

        pixmap = self._pixmap.copy()

        painter = QtGui.QPainter(pixmap)
        painter.setPen(QtGui.QColor(255, 255, 255))
        painter.drawPoint(self.pos_x, self.pos_y)
        painter.end()

        self.setPixmap(pixmap.scaled(384, 93))

    def add_color(self, pixmap):
        mask = pixmap.createMaskFromColor(
            QtGui.QColor(0, 0, 0), QtCore.Qt.MaskOutColor)

        p = QtGui.QPainter(pixmap)
        p.setPen(QtGui.QColor(255, 201, 14))

        p.drawPixmap(pixmap.rect(), mask, mask.rect())
        p.end()

        mask = pixmap.createMaskFromColor(
            QtGui.QColor(255, 255, 255), QtCore.Qt.MaskOutColor)

        p = QtGui.QPainter(pixmap)
        p.setPen(QtGui.QColor(0, 0, 0))
        p.drawPixmap(pixmap.rect(), mask, mask.rect())
        p.end()

        return pixmap

    def save_view_to_file(self, state, name="display"):
        if not os.path.isdir(self.path):
            os.makedirs(self.path)

        timestamp = time.strftime("%Y%m%d%H%M%S")
        filename = '{}_{}.png'.format(name, timestamp)

        self._pixmap.save(os.path.join(self.path, filename), 'PNG')

    def update_display_view(self, image_data):
        self._pixmap.loadFromData(self.format_image_data(bytes(image_data)))

        px = self.add_color(self._pixmap).copy()

        p = QtGui.QPainter(px)
        p.setPen(QtGui.QColor(255, 255, 255))
        p.drawPoint(self.pos_x, self.pos_y)
        p.end()

        self.setPixmap(px.scaled(384, 93))

        if self.isHidden():
            self.show()

    def format_image_data(self, image_data):
        formated_data = []

        data = 0
        bit_cnt = 0
        for y in range(0, 32):
            page_idx = math.floor(y / 8)
            page_offset = y % 8
            byte_offset = VRAM_COLUMNS * page_idx
            for x in range(0, 128):
                if bit_cnt == 8:
                    formated_data.append(data)
                    data = 0
                    bit_cnt = 0

                bit = (image_data[byte_offset + x] >> page_offset) & 0x01
                data = (data | (bit << (7 - bit_cnt)))
                bit_cnt = bit_cnt + 1

        cnt = 0

        img_data = []
        row_data = []
        for byte in formated_data:

            if cnt == 16:
                img_data.append(row_data)
                row_data = []
                cnt = 0

            row_data.append(byte)
            cnt = cnt + 1
        return bytes(create_bitmap_image(img_data, 128))
