Andreasdahlberg/sillycat/software/SerialInterface.py

#!/usr/bin/env python3
# -*- coding: utf-8 -*
#
# This file is part of SillyCat Development Tools.
#
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
import glob

import serial
from PyQt5 import QtCore
from DevToolUtil import platform_is_windows

__author__ = 'andreas.dahlberg90@gmail.com (Andreas Dahlberg)'
__version__ = '0.1.0'


class SerialInterface(QtCore.QThread):
    """Class to listen for serial data"""

    new_vram = QtCore.pyqtSignal(QtCore.QByteArray)
    new_pck = QtCore.pyqtSignal(str)
    new_stream = QtCore.pyqtSignal(str)

    def __init__(self):
        """Init interface"""
        QtCore.QThread.__init__(self)
        self._running = False
        self._ser = None

    def open_port(self, port, baudrate, timeout=0.1):
        """Connect the interface to a serial port"""
        try:
            self._ser = serial.Serial(port, baudrate, timeout=timeout)
            return True
        except serial.SerialException:
            print('Failed to open interface on port ' + port)
            return False

    def get_ports(self):
        """Get a list with all available COM-ports"""

        if platform_is_windows():
            ports = range(256)
        else:
            ports = glob.glob('/dev/tty[A-Za-z]*')

        open_ports = []
        for port_name in ports:
            try:
                tmp_serial = serial.Serial(port_name)
                open_ports.append(tmp_serial.portstr)
                tmp_serial.close()
            except serial.SerialException:
                pass
        return open_ports

    def run(self):
        """Listens for data and emits a signal for every new line"""
        self._running = True
        while self._running:
            rx_data = self._ser.readline()
            if rx_data:
                if rx_data[:6] == b'<VRAM>':
                    rx_data += (self._ser.read(520 - len(rx_data)))
                    self.new_vram.emit(rx_data[6:-2])
                elif rx_data[:5] == b'<PCK>':
                    self.new_pck.emit(rx_data[5:].decode('utf-8').rstrip('\r\n'))
                else:
                    try:
                        self.new_stream.emit(rx_data.decode('utf-8').rstrip('\r\n'))
                    except UnicodeDecodeError:
                        pass
        self.exit_cleanup()

    def stop(self):
        """Stop listen for new data and kill thread"""
        self._running = False

    def exit_cleanup(self):
        """Clean up before killing thread, closing serial port"""
        self._ser.close()
