Andreasdahlberg/sillycat/firmware/src/main/gui/guiRTC.c

/**
 * @file   guiRTC.c
 * @Author Andreas Dahlberg (andreas.dahlberg90@gmail.com)
 * @date   2021-04-11 (Last edit)
 * @brief  Implementation of GUI for displaying the current time.
 */

/*
This file is part of SillyCat firmware.

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
You should have received a copy of the GNU General Public License
along with SillyCat firmware.  If not, see <http://www.gnu.org/licenses/>.
*/

//////////////////////////////////////////////////////////////////////////
//INCLUDES
//////////////////////////////////////////////////////////////////////////

#include "common.h"
#include "libDebug.h"
#include "libUI.h"
#include "Encoder.h"
#include "Interface.h"
#include "RTC.h"
#include "Time.h"
#include "guiRTC.h"

//////////////////////////////////////////////////////////////////////////
//DEFINES
//////////////////////////////////////////////////////////////////////////

#define UTC_OFFSET_SEC 3600

//////////////////////////////////////////////////////////////////////////
//TYPE DEFINITIONS
//////////////////////////////////////////////////////////////////////////

struct module_t
{
    struct
    {
        struct view overview;
        struct view details;
    } view;
    struct
    {
        bool active;
        size_t index;
        struct time_t time;
        struct encoder_callbacks_t callbacks;
    } set_time;
};

struct limits_t
{
    uint8_t max;
    uint8_t min;
};

//////////////////////////////////////////////////////////////////////////
//VARIABLES
//////////////////////////////////////////////////////////////////////////

static struct module_t module;

//////////////////////////////////////////////////////////////////////////
//LOCAL FUNCTION PROTOTYPES
//////////////////////////////////////////////////////////////////////////

static void DrawClockView(uint16_t context __attribute__ ((unused)));
static void DrawDetailedTimeView(uint16_t context __attribute__ ((unused)));
static void DrawUnderLine(void);
static void DrawSetTimeView(uint16_t context __attribute__ ((unused)));
static void ConvertTimeToLocal(struct time_t *time_p);
static void ConvertTimeToUTC(struct time_t *time_p);
static void SetTimeAction(uint16_t context __attribute__ ((unused)));
static struct limits_t GetCurrentFieldLimits(size_t field_index, const struct time_t *time_p);
static void AdjustTimeToLimits(const struct time_t *time_p);
static void IncreaseField(void);
static void DecreaseField(void);

//////////////////////////////////////////////////////////////////////////
//FUNCTIONS
//////////////////////////////////////////////////////////////////////////

void guiRTC_Init(void)
{
    module.set_time.active = false;
    module.set_time.index = 0;

    Interface_InitView(&module.view.overview, DrawClockView, 0);
    Interface_AddView(&module.view.overview);

    Interface_InitView(&module.view.details, DrawDetailedTimeView, 0);
    Interface_AddAction(&module.view.details, SetTimeAction);
    Interface_AddChild(&module.view.overview, &module.view.details);

    INFO("Initialized RTC view.");
}

//////////////////////////////////////////////////////////////////////////
//LOCAL FUNCTIONS
//////////////////////////////////////////////////////////////////////////

static void DrawClockView(uint16_t context __attribute__ ((unused)))
{
    struct time_t time;
    RTC_GetCurrentTime(&time);

    ConvertTimeToLocal(&time);

    libUI_Print("%02u:%02u", 45, UI_SINGLE_ROW, time.hour, time.minute);
}

static void DrawDetailedTimeView(uint16_t context __attribute__ ((unused)))
{
    struct time_t time;
    RTC_GetCurrentTime(&time);

    ConvertTimeToLocal(&time);

    libUI_Print("20%02u-%02u-%02u", 25, UI_DOUBLE_ROW_FIRST, time.year, time.month, time.date);
    libUI_Print("%02u:%02u:%02u", 34, UI_DOUBLE_ROW_SECOND, time.hour, time.minute, time.second);
}

static void DrawUnderLine(void)
{
    struct underline_t
    {
        uint8_t x;
        uint8_t y;
        uint8_t length;
    };

    const struct underline_t lines[6] =
    {
        {
            .x = 25,
            .y = UI_DOUBLE_ROW_FIRST + 1,
            .length = 32
        },
        {
            .x = 65,
            .y = UI_DOUBLE_ROW_FIRST + 1,
            .length = 16
        },
        {
            .x = 89,
            .y = UI_DOUBLE_ROW_FIRST + 1,
            .length = 16
        },
        {
            .x = 34,
            .y = UI_DOUBLE_ROW_SECOND + 1,
            .length = 16
        },
        {
            .x = 58,
            .y = UI_DOUBLE_ROW_SECOND + 1,
            .length = 16
        },
        {
            .x = 82,
            .y = UI_DOUBLE_ROW_SECOND + 1,
            .length = 16
        },
    };

    const struct underline_t *line_p = &lines[module.set_time.index];

    libUI_DrawLine(line_p->x, line_p->y, line_p->x + line_p->length, line_p->y);
}

static void DrawSetTimeView(uint16_t context __attribute__ ((unused)))
{
    struct time_t time;
    time = module.set_time.time;

    libUI_Print("20%02u-%02u-%02u", 25, UI_DOUBLE_ROW_FIRST, time.year, time.month, time.date);
    libUI_Print("%02u:%02u:%02u", 34, UI_DOUBLE_ROW_SECOND, time.hour, time.minute, time.second);

    DrawUnderLine();
}

static void ConvertTimeToLocal(struct time_t *time_p)
{
    uint32_t timestamp = Time_ConvertToTimestamp(time_p);
    timestamp += UTC_OFFSET_SEC;
    *time_p = Time_ConvertFromTimestamp(timestamp);
}

static void ConvertTimeToUTC(struct time_t *time_p)
{
    uint32_t timestamp = Time_ConvertToTimestamp(time_p);
    timestamp -= timestamp >= UTC_OFFSET_SEC ? UTC_OFFSET_SEC : timestamp;
    *time_p = Time_ConvertFromTimestamp(timestamp);
}

static void NextField(void)
{
    if (module.set_time.index < 5)
    {
        ++module.set_time.index;
    }
    else
    {
        module.set_time.index = 0;
    }

    /**
     * Call refresh so that the underline marking the current field is updated
     * immediately.
     */
    Interface_Refresh();
}

static struct limits_t GetCurrentFieldLimits(
    size_t field_index,
    const struct time_t *time_p)
{
    struct limits_t limits;

    switch (field_index)
    {
        case 0:
            limits.max = 99;
            limits.min = 0;
            break;

        case 1:
            limits.max = 12;
            limits.min = 1;
            break;

        case 2:
            limits.max = Time_GetDaysInMonth(time_p);
            limits.min = 1;
            break;

        case 3:
            limits.max = 23;
            limits.min = 0;
            break;

        case 4:
        case 5:
            limits.max = 59;
            limits.min = 0;
            break;

        default:
            sc_assert_fail();
    }

    return limits;
}

static void AdjustTimeToLimits(const struct time_t *time_p)
{
    for (size_t i = 0; i < sizeof(*time_p); ++i)
    {
        struct limits_t limits = GetCurrentFieldLimits(i, time_p);

        uint8_t *field_p = ((uint8_t *)&module.set_time.time) + i;

        if (*field_p > limits.max)
        {
            *field_p = limits.max;
        }
        else if (*field_p < limits.min)
        {
            *field_p = limits.min;
        }
    }
}

static void IncreaseField(void)
{
    uint8_t *field_p = ((uint8_t *)&module.set_time.time) + module.set_time.index;

    struct limits_t limits;
    limits = GetCurrentFieldLimits(module.set_time.index, &module.set_time.time);

    if (*field_p < limits.max)
    {
        *field_p += 1;
    }
    else
    {
        *field_p = limits.min;
    }
    AdjustTimeToLimits(&module.set_time.time);

    /**
     * Call refresh so that the updated value is updated immediately.
     */
    Interface_Refresh();
}

static void DecreaseField(void)
{
    uint8_t *field_p = ((uint8_t *)&module.set_time.time) + module.set_time.index;

    struct limits_t limits;
    limits = GetCurrentFieldLimits(module.set_time.index, &module.set_time.time);

    if (*field_p > limits.min)
    {
        *field_p -= 1;
    }
    else
    {
        *field_p = limits.max;
    }
    AdjustTimeToLimits(&module.set_time.time);

    /**
     * Call refresh so that the updated value is updated immediately.
     */
    Interface_Refresh();
}

static void SetTimeAction(uint16_t context __attribute__ ((unused)))
{
    if (module.set_time.active)
    {
        /**
         * The callbacks need to be restored to the default functions
         * so that the user can leave the 'set time' view.
         */
        Encoder_SetCallbacks(&module.set_time.callbacks);

        ConvertTimeToUTC(&module.set_time.time);
        RTC_SetCurrentTime(&module.set_time.time);

        module.view.details.draw_function = DrawDetailedTimeView;
        module.set_time.active = false;

        INFO("New time set");
    }
    else
    {
        /**
         * Hijack the input callbacks so that they are used to change the
         * time instead of navigation. Store the old callbacks so that
         * they can be restored when the time is set.
         */
        module.set_time.callbacks = Encoder_GetCallbacks();
        const struct encoder_callbacks_t encoder_callbacks =
        {
            .right = IncreaseField,
            .left = DecreaseField,
            .brief_push = NextField,
            .extended_push = Interface_Action
        };
        Encoder_SetCallbacks(&encoder_callbacks);

        RTC_GetCurrentTime(&module.set_time.time);
        ConvertTimeToLocal(&module.set_time.time);

        module.view.details.draw_function = DrawSetTimeView;
        module.set_time.active = true;
        module.set_time.index = 0;
    }
}
